OOHQ3E/smarthome/Docs/uml diagram/ENG_extended UML diagram.png

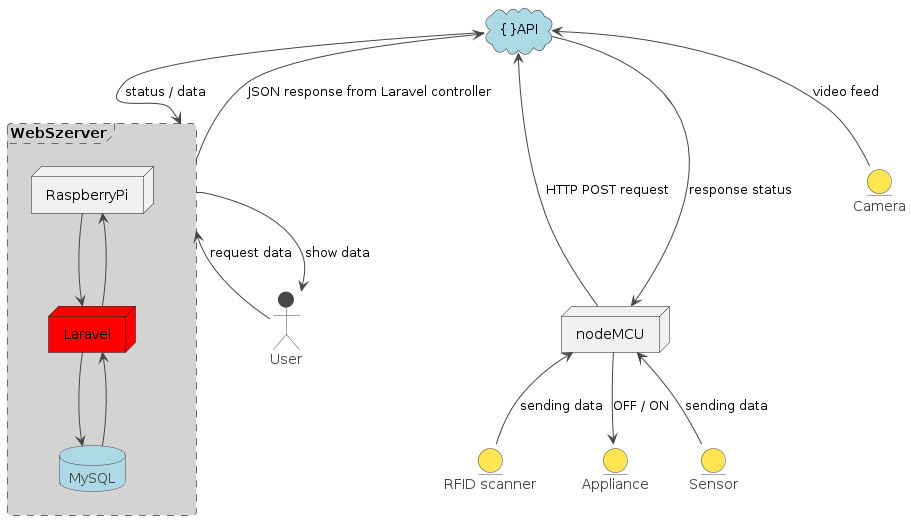
Docs/uml diagram/ENG_extended UML diagram.png
